samayc16/Capstone/PCB/core/noi2c-pcb.png

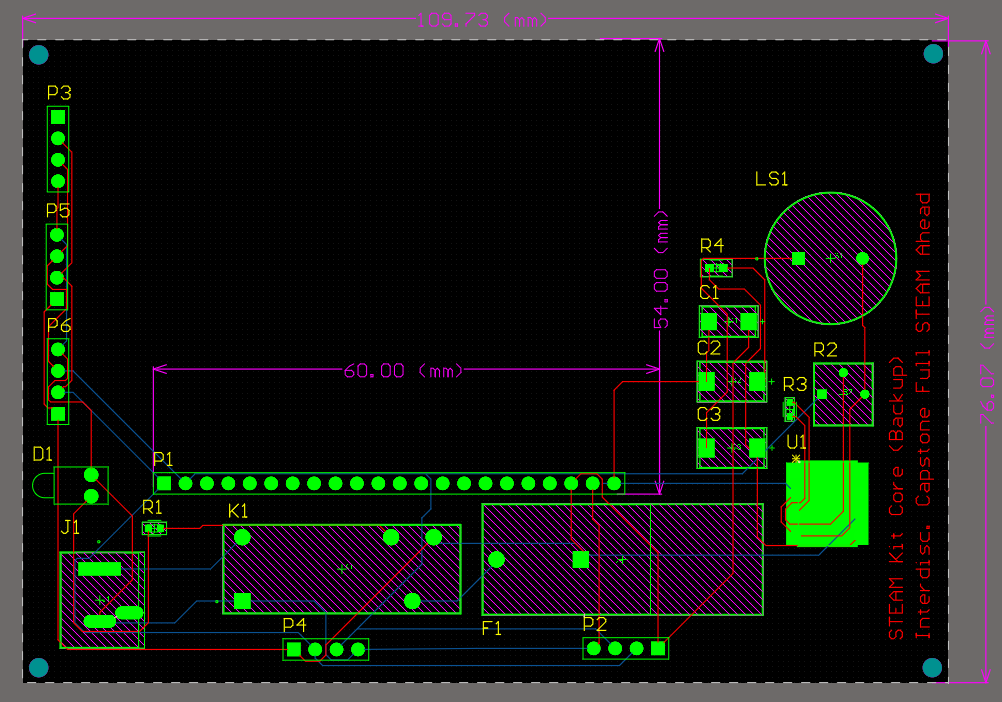
PCB/core/noi2c-pcb.png
