samayc16/Capstone/PCB/core/pcbdraft1.png

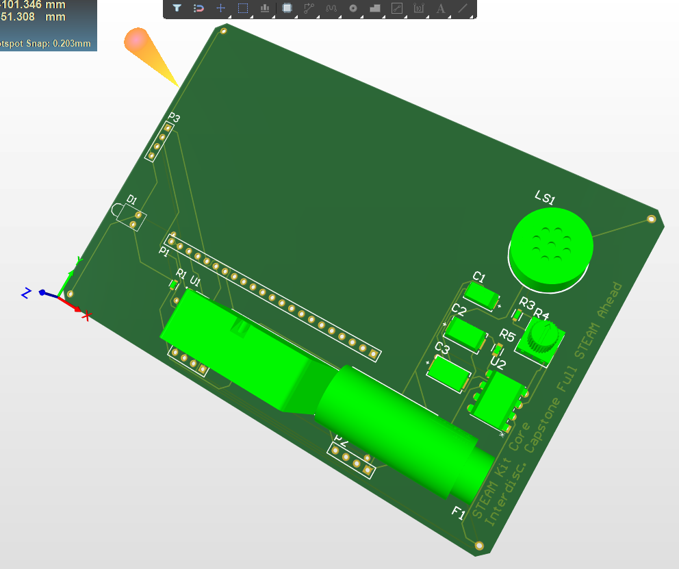
PCB/core/pcbdraft1.png
