samayc16/Capstone/PCB/core/pcbdraft2-dimfix.png

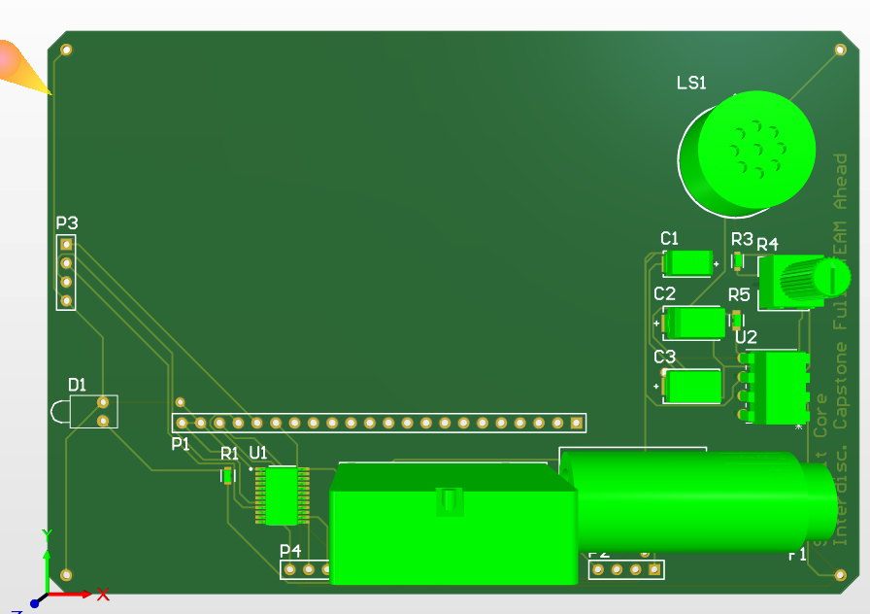
PCB/core/pcbdraft2-dimfix.png
