samayc16/Capstone/PCB/core/pcbdraft-routing.png

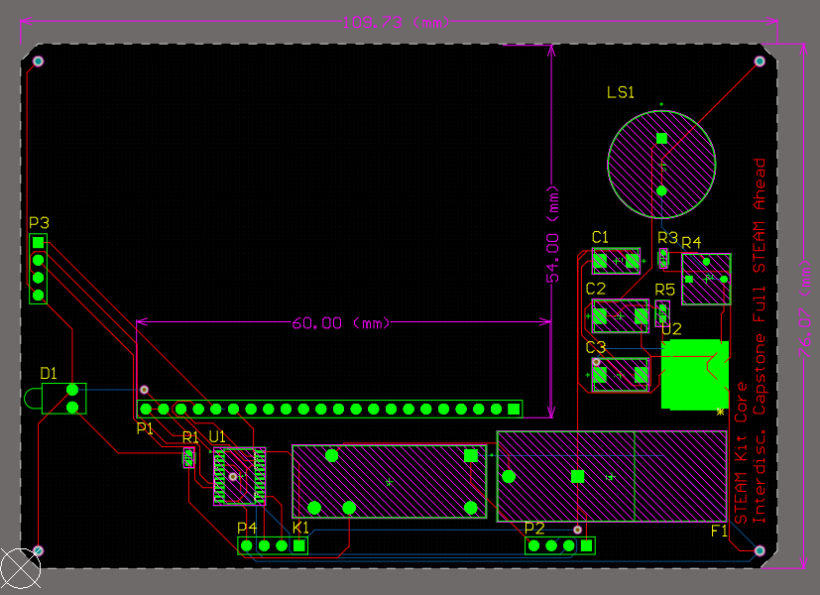
PCB/core/pcbdraft-routing.png
