samayc16/Capstone/Motor CAD/Motor Module V3 Bottom.SLDPRT

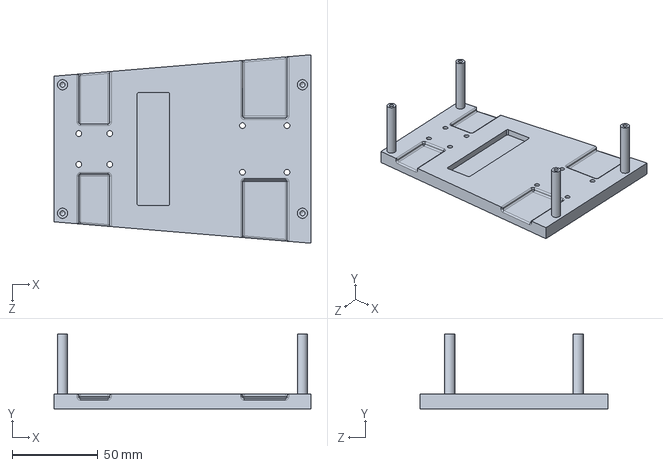
[picture p33: CAD file, 2023-12-12]
Motor CAD/Motor Module V3 Bottom.SLDPRT
150.0 x 43.5 x 110.0 mm
