samayc16/Capstone/Motor CAD/STL/Front chassis - Frame/Wishbone Front Lower Left.stl

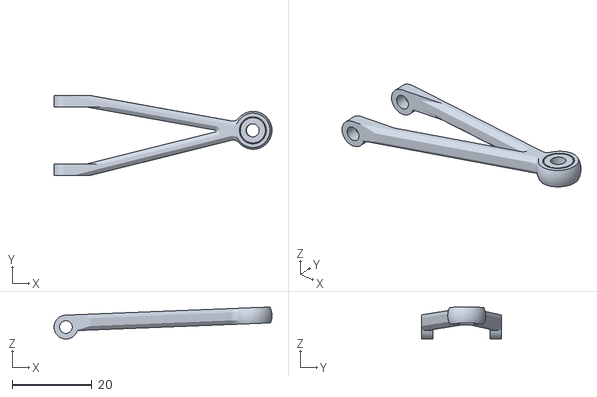
[picture p34: CAD file, 2023-12-12]
Motor CAD/STL/Front chassis - Frame/Wishbone Front Lower Left.stl
54.8 x 20.0 x 8.04
