samayc16/Capstone/Motor CAD/STL/Front chassis - Steering/Steering Parts.3mf

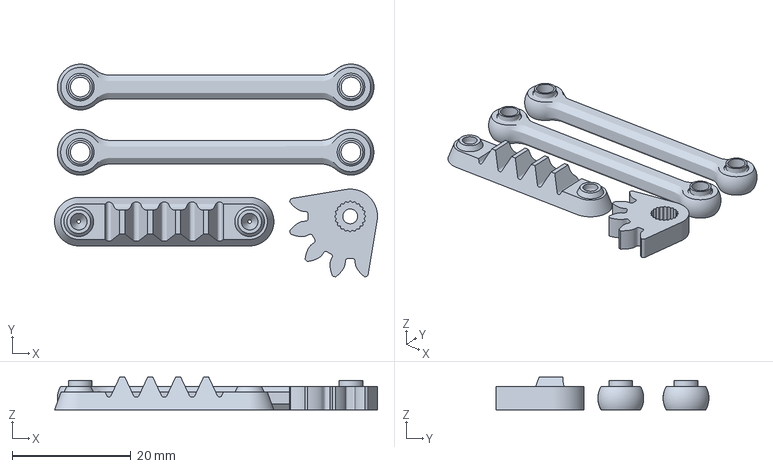
[picture p35: CAD file, 2023-12-12]
Motor CAD/STL/Front chassis - Steering/Steering Parts.3mf
54.5 x 35.9 x 5.56 mm
