samayc16/Capstone/Motor CAD/STL/Rear chassis - Differential/Pinion Gear.stl

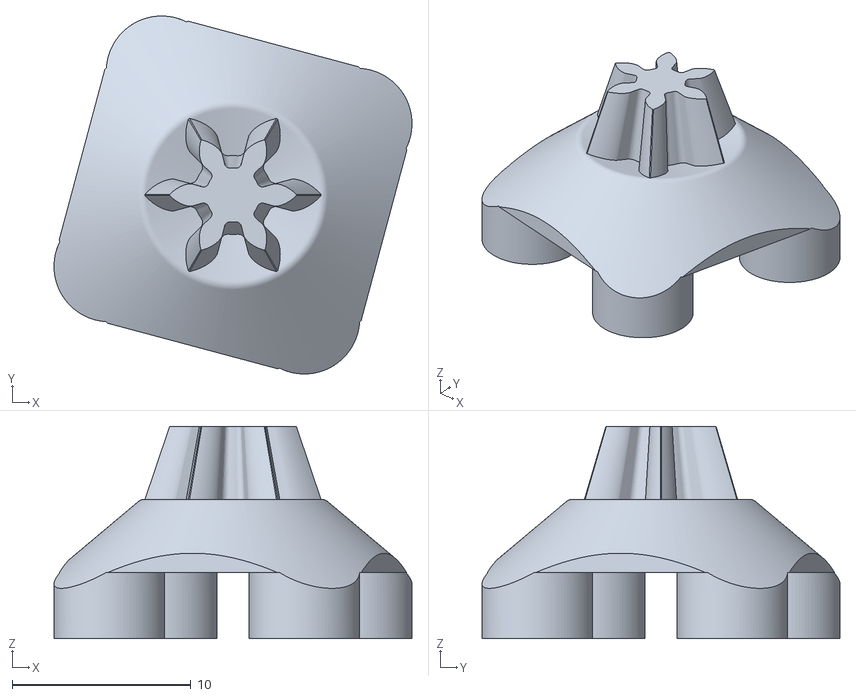
[picture p36: CAD file, 2023-12-12]
Motor CAD/STL/Rear chassis - Differential/Pinion Gear.stl
20.1 x 20.1 x 11.9
