samayc16/Capstone/Motor CAD/STL/Rear chassis - Frame/Rear Frame and Knuckles.3mf

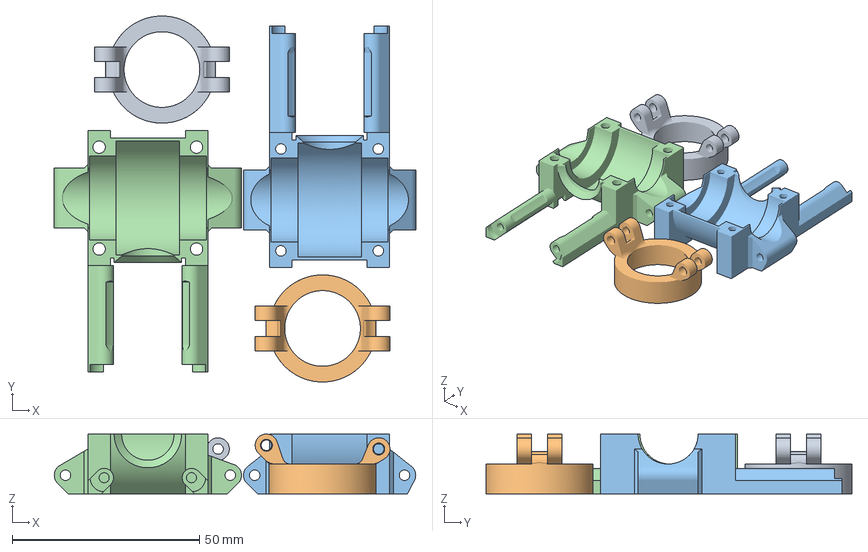
[picture p37: CAD file, 2023-12-12]
Motor CAD/STL/Rear chassis - Frame/Rear Frame and Knuckles.3mf
96.5 x 97.7 x 16.0 mm
Rear Frame and Knuckles.3mf(2)
Rear Frame and Knuckles.3mf(3)
Frame Rear Bottom.stl
Frame Rear Top.stl
