samayc16/Capstone/Motor CAD/STL/Front chassis - Frame/Frame Front Bottom.stl

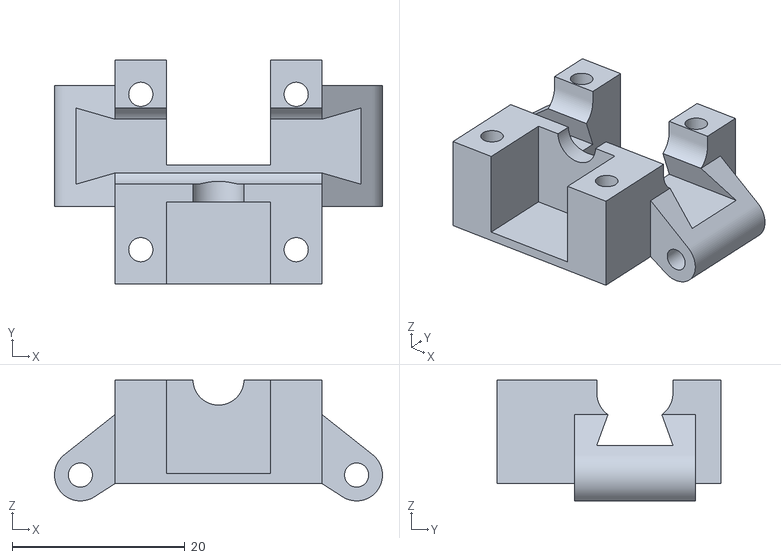
[picture p38: CAD file, 2023-12-12]
Motor CAD/STL/Front chassis - Frame/Frame Front Bottom.stl
38.0 x 26.0 x 14.0
