samayc16/Capstone/Motor CAD/STL/Front chassis - Steering/Front Axle.3mf

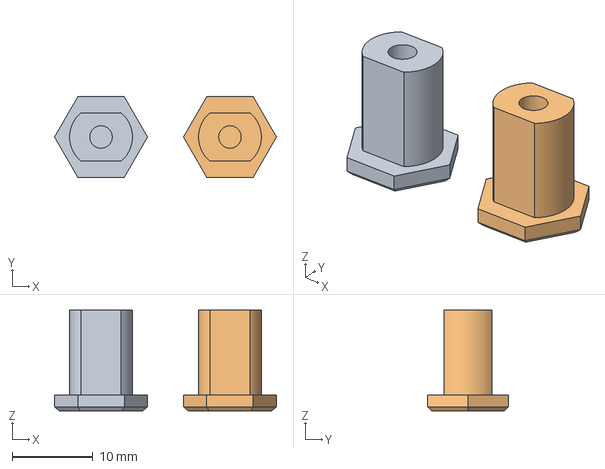
[picture p39: CAD file, 2023-12-12]
Motor CAD/STL/Front chassis - Steering/Front Axle.3mf
27.5 x 10.00 x 12.5 mm
Axle Front (X2).stl
Axle Front (X2).stl(1)
