samayc16/Capstone/Motor CAD/STL/Rear chassis - Axle shaft/Center Joint (X4).stl

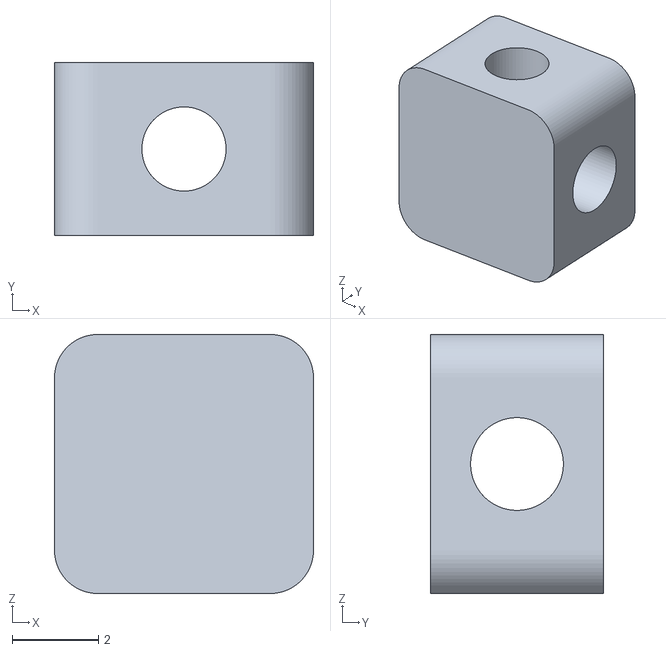
[picture p40: CAD file, 2023-12-12]
Motor CAD/STL/Rear chassis - Axle shaft/Center Joint (X4).stl
6.00 x 4.00 x 6.00
