samayc16/Capstone/Motor CAD/STL/Rear chassis - Differential/Drive Gear (X2).stl

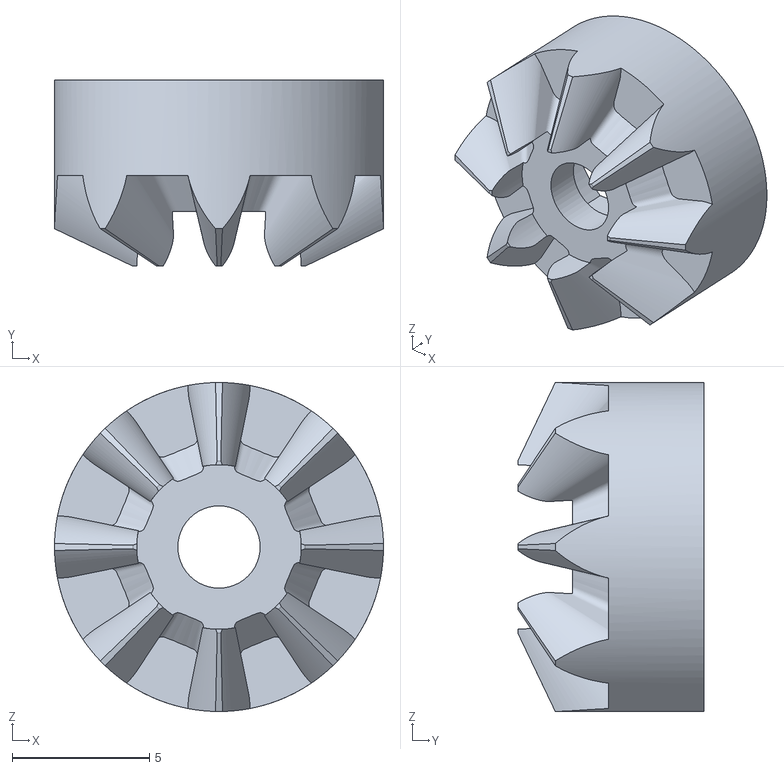
[picture p41: CAD file, 2023-12-12]
Motor CAD/STL/Rear chassis - Differential/Drive Gear (X2).stl
12.0 x 6.80 x 12.0
