samayc16/Capstone/Motor CAD/STL/Rear chassis - Frame/Rear spring.stl

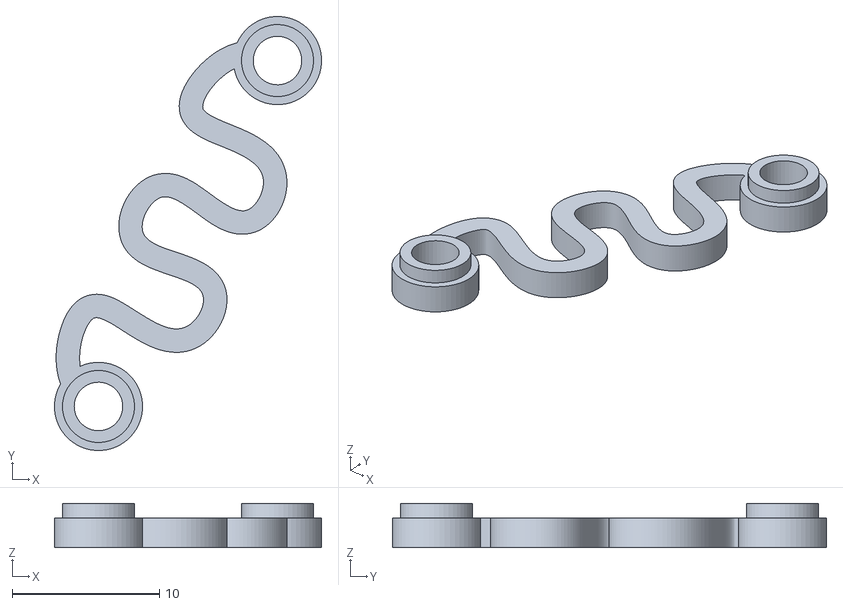
[picture p42: CAD file, 2023-12-12]
Motor CAD/STL/Rear chassis - Frame/Rear spring.stl
18.2 x 29.5 x 3.00
