samayc16/Capstone/Motor CAD/STL/Front chassis - Frame/Knuckle Front Right.stl

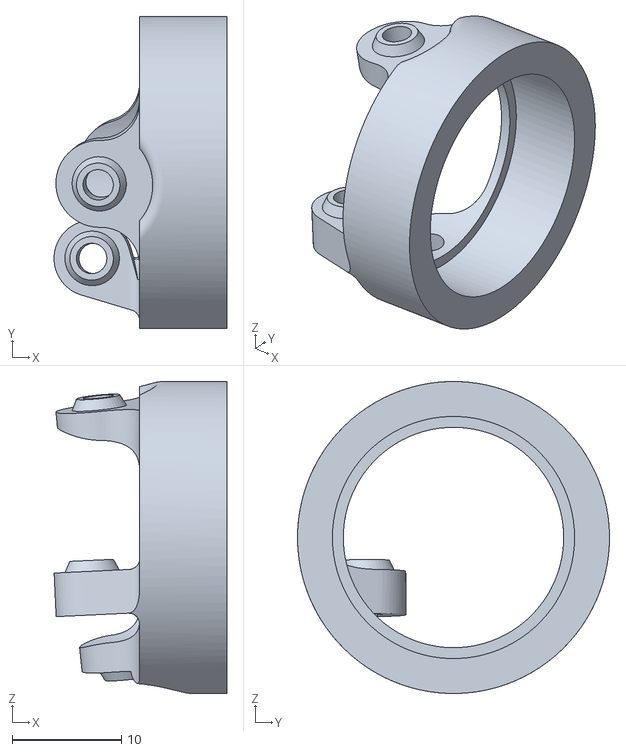
[picture p43: CAD file, 2023-12-12]
Motor CAD/STL/Front chassis - Frame/Knuckle Front Right.stl
15.8 x 28.6 x 28.6
