samayc16/Capstone/Motor CAD/STL/Front chassis - Steering/Axle Front (X2).stl

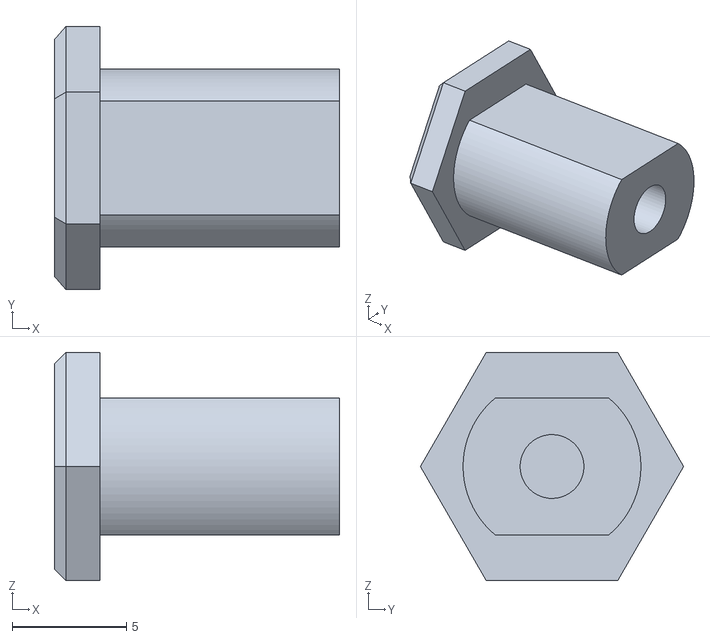
[picture p44: CAD file, 2023-12-12]
Motor CAD/STL/Front chassis - Steering/Axle Front (X2).stl
12.5 x 11.5 x 10.0
