samayc16/Capstone/Motor CAD/STL/Rear chassis - Axle shaft/U Joint Shaft (X4).stl

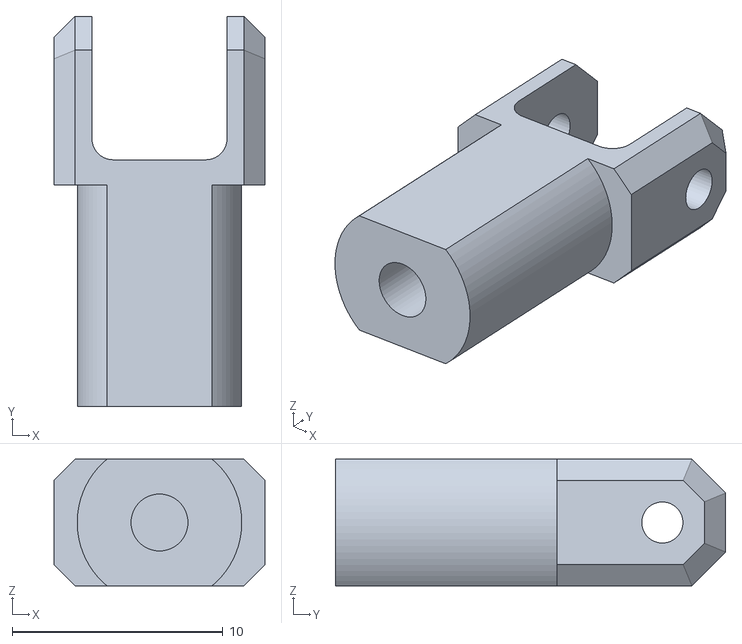
[picture p45: CAD file, 2023-12-12]
Motor CAD/STL/Rear chassis - Axle shaft/U Joint Shaft (X4).stl
10.0 x 18.5 x 6.00
