samayc16/Capstone/Motor CAD/STL/Rear chassis - Differential/Spider Gear (X2).stl

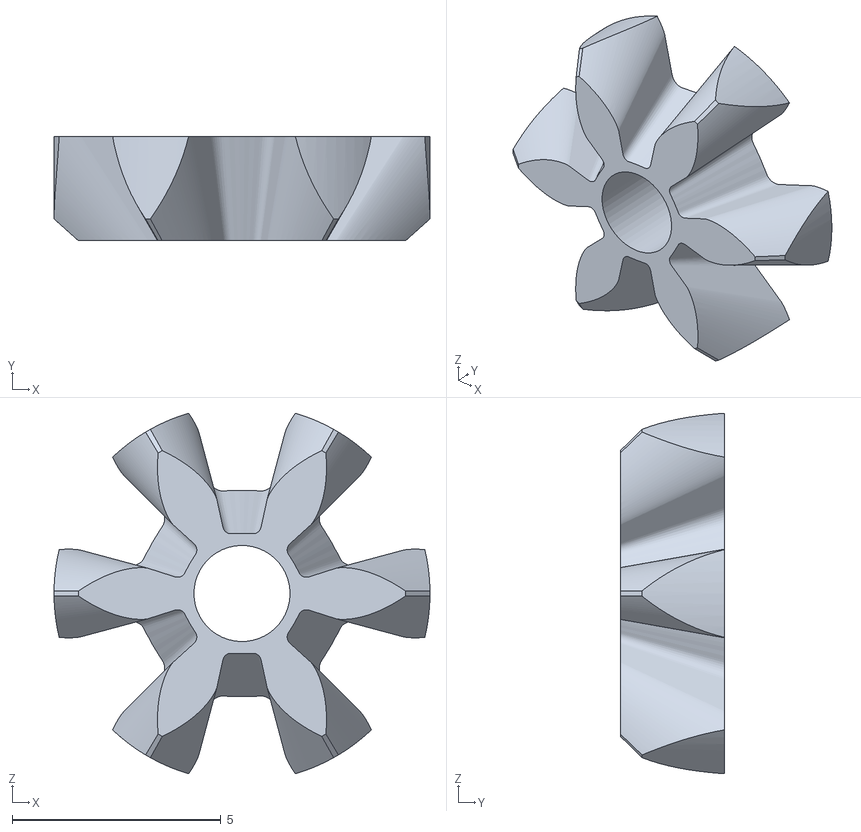
[picture p46: CAD file, 2023-12-12]
Motor CAD/STL/Rear chassis - Differential/Spider Gear (X2).stl
9.00 x 2.50 x 8.63
