samayc16/Capstone/Motor CAD/STL/Rear chassis - Frame/Frame Rear Top.stl

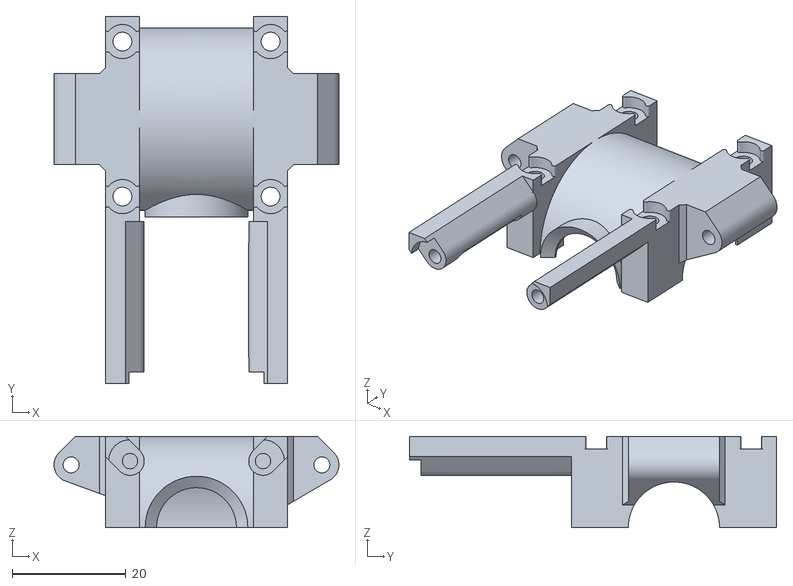
[picture p47: CAD file, 2023-12-12]
Motor CAD/STL/Rear chassis - Frame/Frame Rear Top.stl
50.0 x 64.4 x 16.0
