samayc16/Capstone/CAD/3DPrintFabricationPlate.SLDPRT

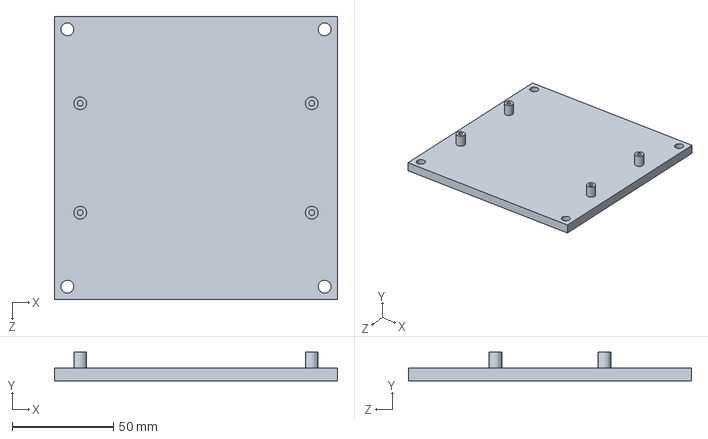
[picture p48: CAD file, 2023-10-20]
CAD/3DPrintFabricationPlate.SLDPRT
139.7 x 14.3 x 139.7 mm
