samayc16/Capstone/Motor CAD/STL/Front chassis - Frame/Front Wishbones.3mf

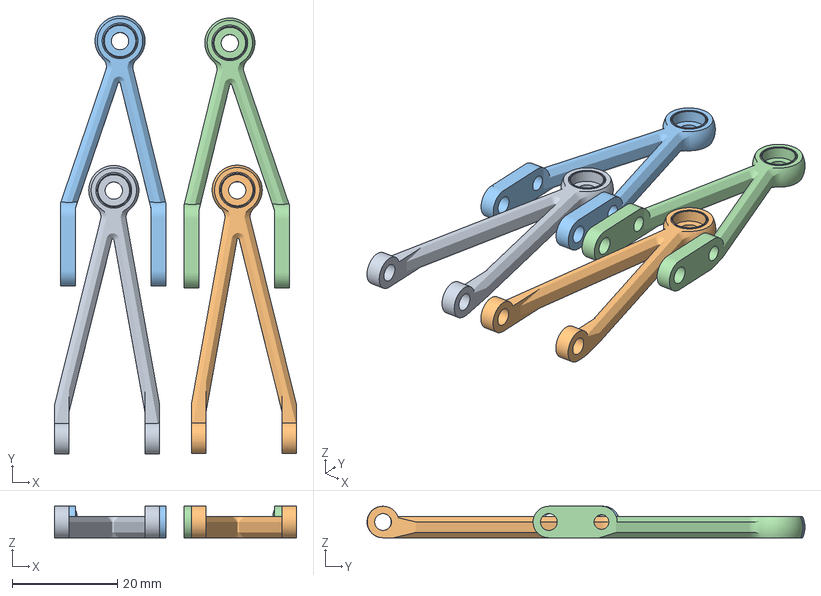
[picture p49: CAD file, 2023-12-12]
Motor CAD/STL/Front chassis - Frame/Front Wishbones.3mf
46.1 x 83.3 x 6.00 mm
wishbone tension front lower left.stl
wishbone tension front lower right.stl
wishbone tension front upper left.stl
wishbone tension front upper right.stl
