samayc16/Capstone/Motor CAD/STL/Front chassis - Steering/Pinion.stl

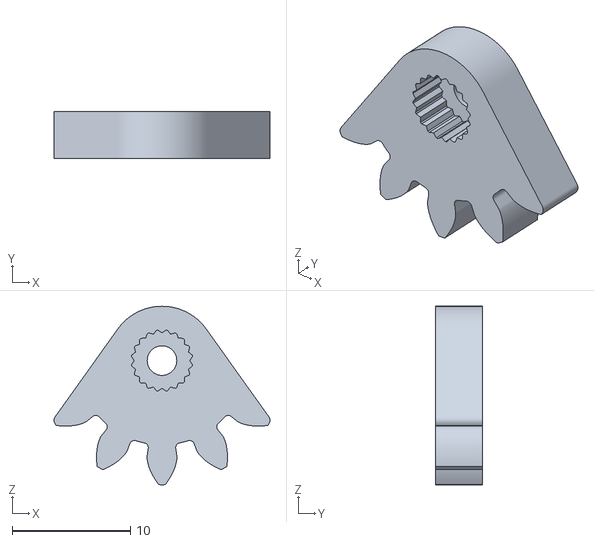
[picture p50: CAD file, 2023-12-12]
Motor CAD/STL/Front chassis - Steering/Pinion.stl
18.3 x 4.00 x 15.1
