samayc16/Capstone/Motor CAD/STL/Rear chassis - Axle shaft/U Joint Telescopic Shaft (X2).stl

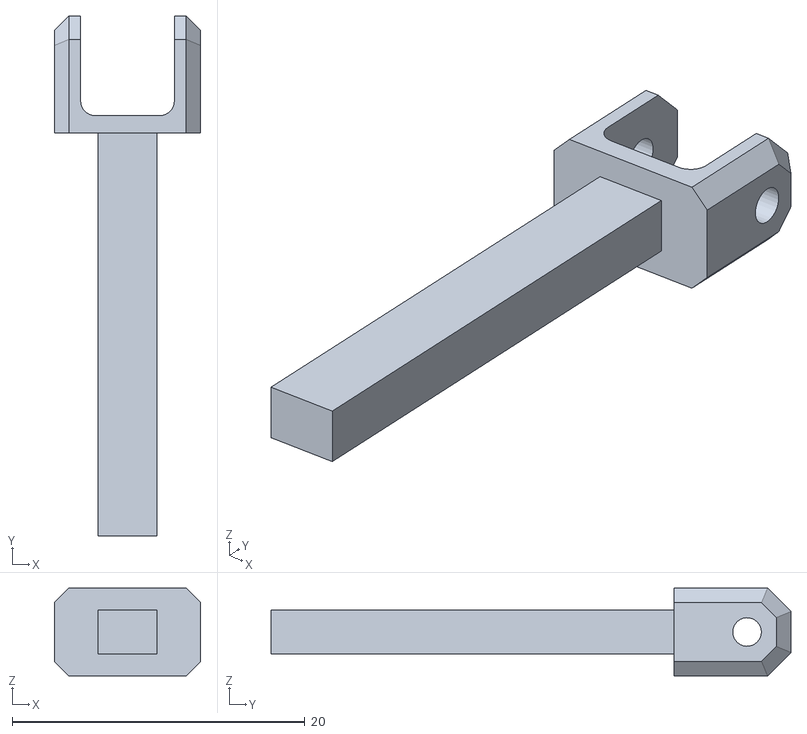
[picture p51: CAD file, 2023-12-12]
Motor CAD/STL/Rear chassis - Axle shaft/U Joint Telescopic Shaft (X2).stl
10.0 x 35.5 x 6.00
