samayc16/Capstone/Motor CAD/STL/Rear chassis - Frame/Rear Wishbones.3mf

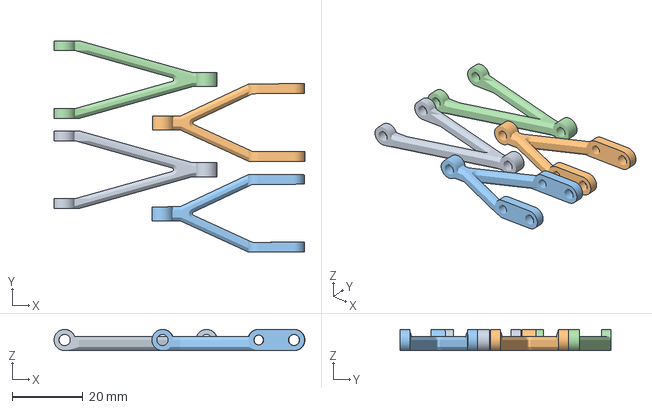
[picture p52: CAD file, 2023-12-12]
Motor CAD/STL/Rear chassis - Frame/Rear Wishbones.3mf
71.1 x 59.9 x 6.01 mm
wishbone tension rear lower (X2).stl x 2
wishbone tension rear upper (X2).stl x 2
