samayc16/Capstone/CAD/TIMicrocontrollerEssentialDimensions.SLDPRT

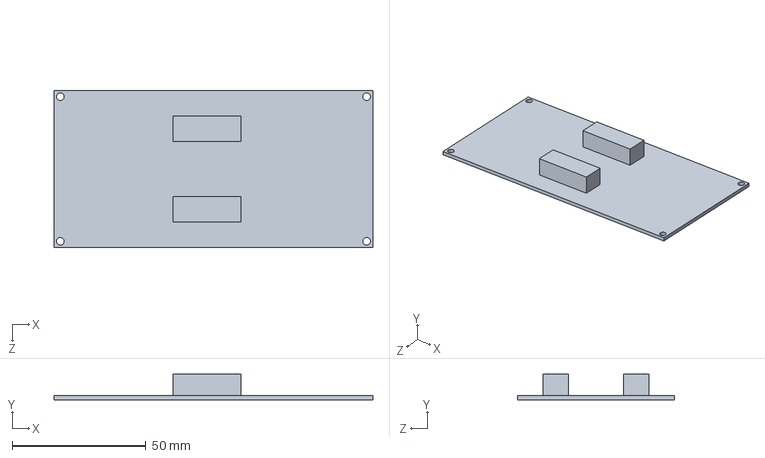
[picture p53: CAD file, 2023-10-20]
CAD/TIMicrocontrollerEssentialDimensions.SLDPRT
119.1 x 9.53 x 58.7 mm
