samayc16/Capstone/Motor CAD/STL/Front chassis - Frame/Front Frame and Knuckles.3mf

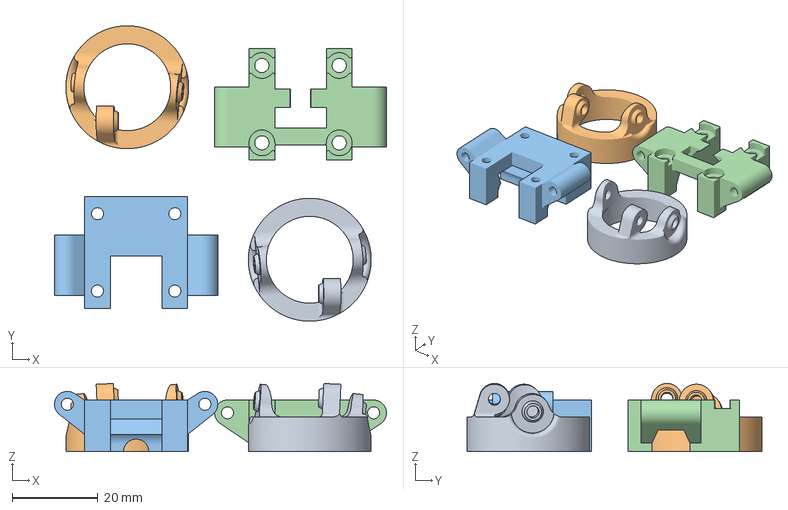
[picture p54: CAD file, 2023-12-12]
Motor CAD/STL/Front chassis - Frame/Front Frame and Knuckles.3mf
77.3 x 68.7 x 15.8 mm
Front Frame and Knuckles.3mf(2)
Front Frame and Knuckles.3mf(3)
Frame Front Bottom.stl
Frame Front Top.stl
