samayc16/Capstone/Motor CAD/STL/Front chassis - Steering/Steering Rack.stl

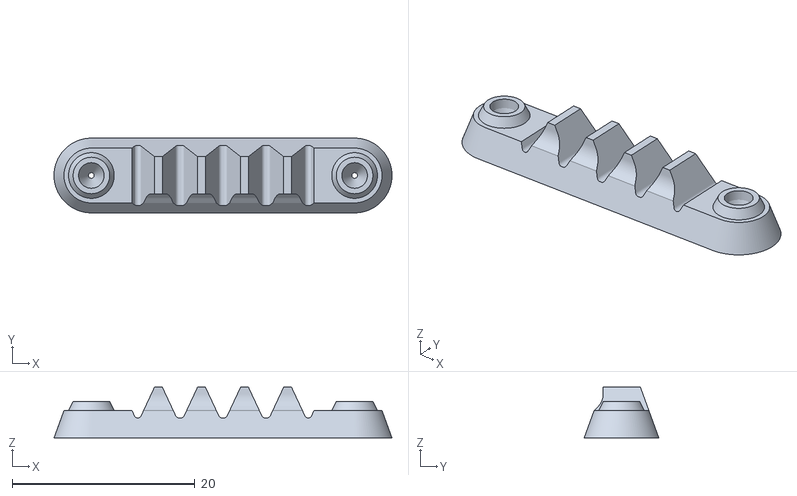
[picture p55: CAD file, 2023-12-12]
Motor CAD/STL/Front chassis - Steering/Steering Rack.stl
37.0 x 8.18 x 5.56
