samayc16/Capstone/Motor CAD/STL/Rear chassis - Frame/Wishbone Rear Lower (X2).stl

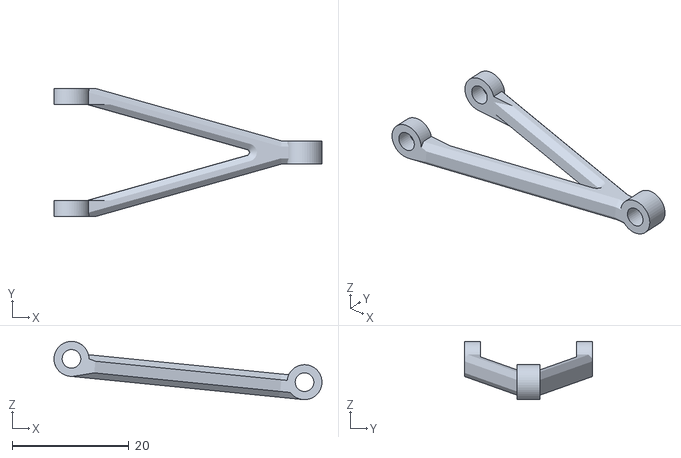
[picture p56: CAD file, 2023-12-12]
Motor CAD/STL/Rear chassis - Frame/Wishbone Rear Lower (X2).stl
46.0 x 22.0 x 9.99
