samayc16/Capstone/Motor CAD/STL/Rear chassis - Frame/Frame Rear Bottom.stl

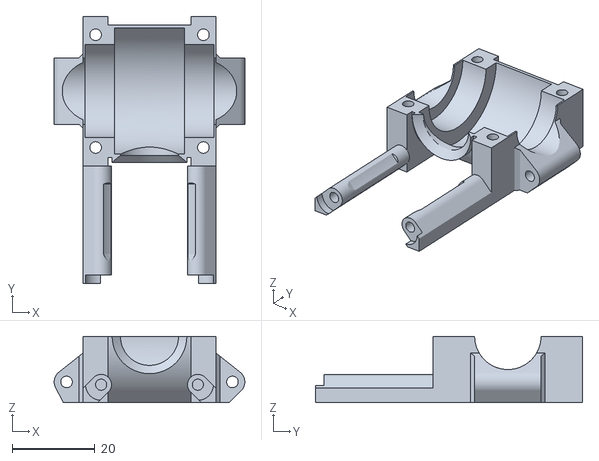
[picture p57: CAD file, 2023-12-12]
Motor CAD/STL/Rear chassis - Frame/Frame Rear Bottom.stl
46.0 x 64.4 x 16.0
