samayc16/Capstone/Motor CAD/STL/Front chassis - Frame/Wishbone Front Upper Left.stl

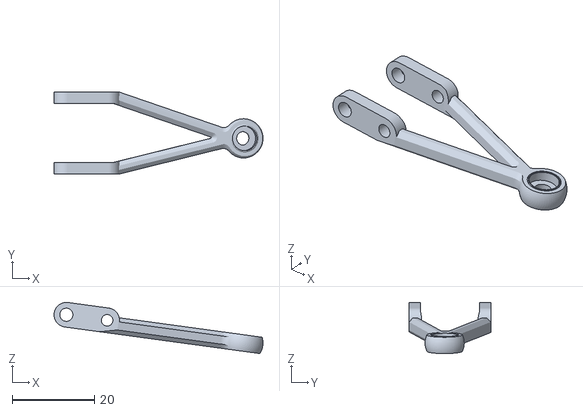
[picture p58: CAD file, 2023-12-12]
Motor CAD/STL/Front chassis - Frame/Wishbone Front Upper Left.stl
50.8 x 20.0 x 12.4
