samayc16/Capstone/Motor CAD/STL/Rear chassis - Frame/Wishbone Rear Upper (X2).stl

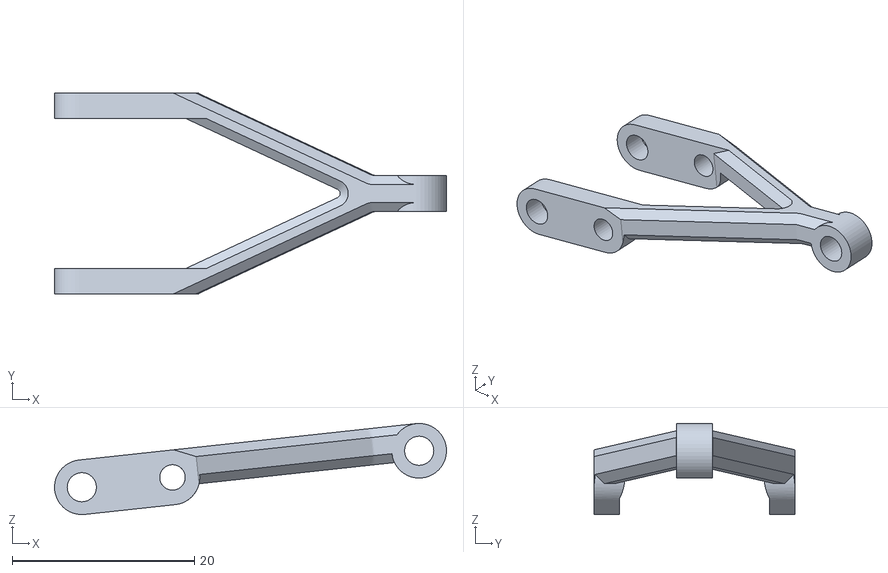
[picture p59: CAD file, 2023-12-12]
Motor CAD/STL/Rear chassis - Frame/Wishbone Rear Upper (X2).stl
43.0 x 22.0 x 9.99
