samayc16/Capstone/Motor CAD/STL/Rear chassis - Frame/Rear Springs.3mf

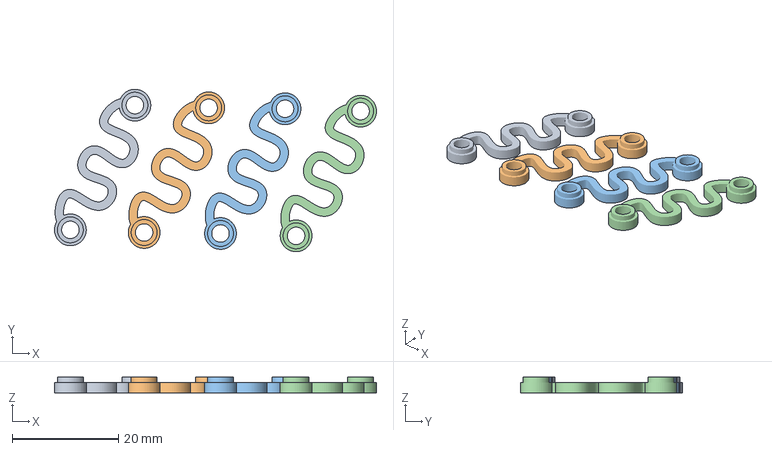
[picture p60: CAD file, 2023-12-12]
Motor CAD/STL/Rear chassis - Frame/Rear Springs.3mf
60.7 x 30.6 x 3.00 mm
spring tension rear (x4).stl x 4
