samayc16/Capstone/Motor CAD/STL/Front chassis - Frame/Front spring.stl

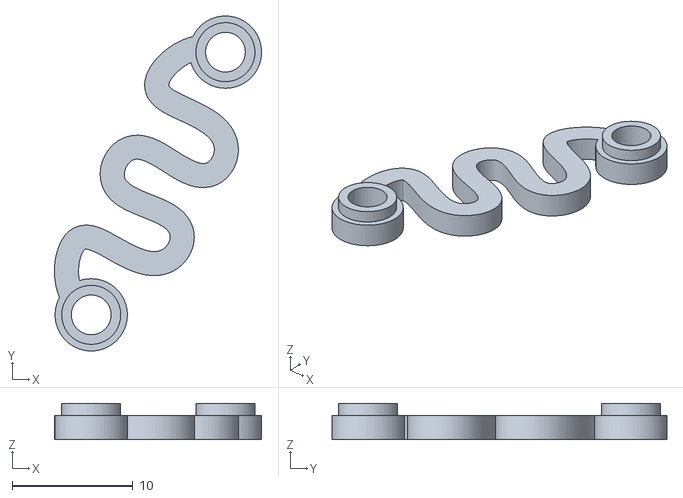
[picture p61: CAD file, 2023-12-12]
Motor CAD/STL/Front chassis - Frame/Front spring.stl
17.2 x 27.8 x 3.00
