samayc16/Capstone/Motor CAD/STL/Front chassis - Frame/Frame Front Top.stl

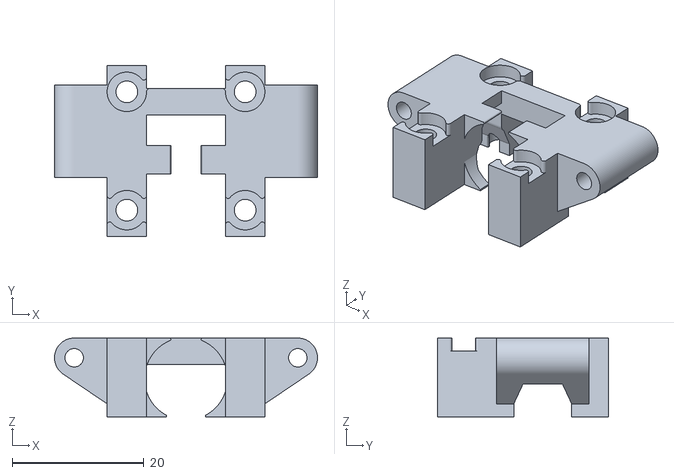
[picture p62: CAD file, 2023-12-12]
Motor CAD/STL/Front chassis - Frame/Frame Front Top.stl
40.0 x 26.0 x 12.0
